Magic-Master420/Wireless-Control-System/Code/RelayPushButton/RelayPushButton.ino

/*
  Blink

  Turns an LED on for one second, then off for one second, repeatedly.

  Most Arduinos have an on-board LED you can control. On the UNO, MEGA and ZERO
  it is attached to digital pin 13, on MKR1000 on pin 6. LED_BUILTIN is set to
  the correct LED pin independent of which board is used.
  If you want to know what pin the on-board LED is connected to on your Arduino
  model, check the Technical Specs of your board at:
  https://www.arduino.cc/en/Main/Products

  modified 8 May 2014
  by Scott Fitzgerald
  modified 2 Sep 2016
  by Arturo Guadalupi
  modified 8 Sep 2016
  by Colby Newman

  This example code is in the public domain.

  https://www.arduino.cc/en/Tutorial/BuiltInExamples/Blink
*/

int pushButtonMiddle = 17;
int pushButtonMiddleStatus = 0;
int relay1Pin = 7;
int relay1State = 0;

// the setup function runs once when you press reset or power the board
void setup() {
  // initialize digital pin LED_BUILTIN as an output.
  Serial.begin(115200);
  pinMode(pushButtonMiddle, INPUT);  // Set the pin as input
  pinMode(relay1Pin, OUTPUT);
  digitalWrite(relay1Pin, LOW);
}

// the loop function runs over and over again forever
void loop() {
  pushButtonMiddleStatus = digitalRead(pushButtonMiddle);  // Read the digital level (0 or 1)
  Serial.println(pushButtonMiddleStatus);
  
  if(pushButtonMiddleStatus){
    (relay1State == 1) ? digitalWrite(relay1Pin, LOW) : digitalWrite(relay1Pin, HIGH);
    (relay1State == 1) ? relay1State = 0 : relay1State = 1;
  }

  delay(500);
}
